jondurrant/IoTFanControlerW5000/schematic/IoTFanControl/IoTFanControl.kicad_sch

## KiCad design schematic/IoTFanControl/IoTFanControl.kicad_sch (2022-04-07, an earlier design)

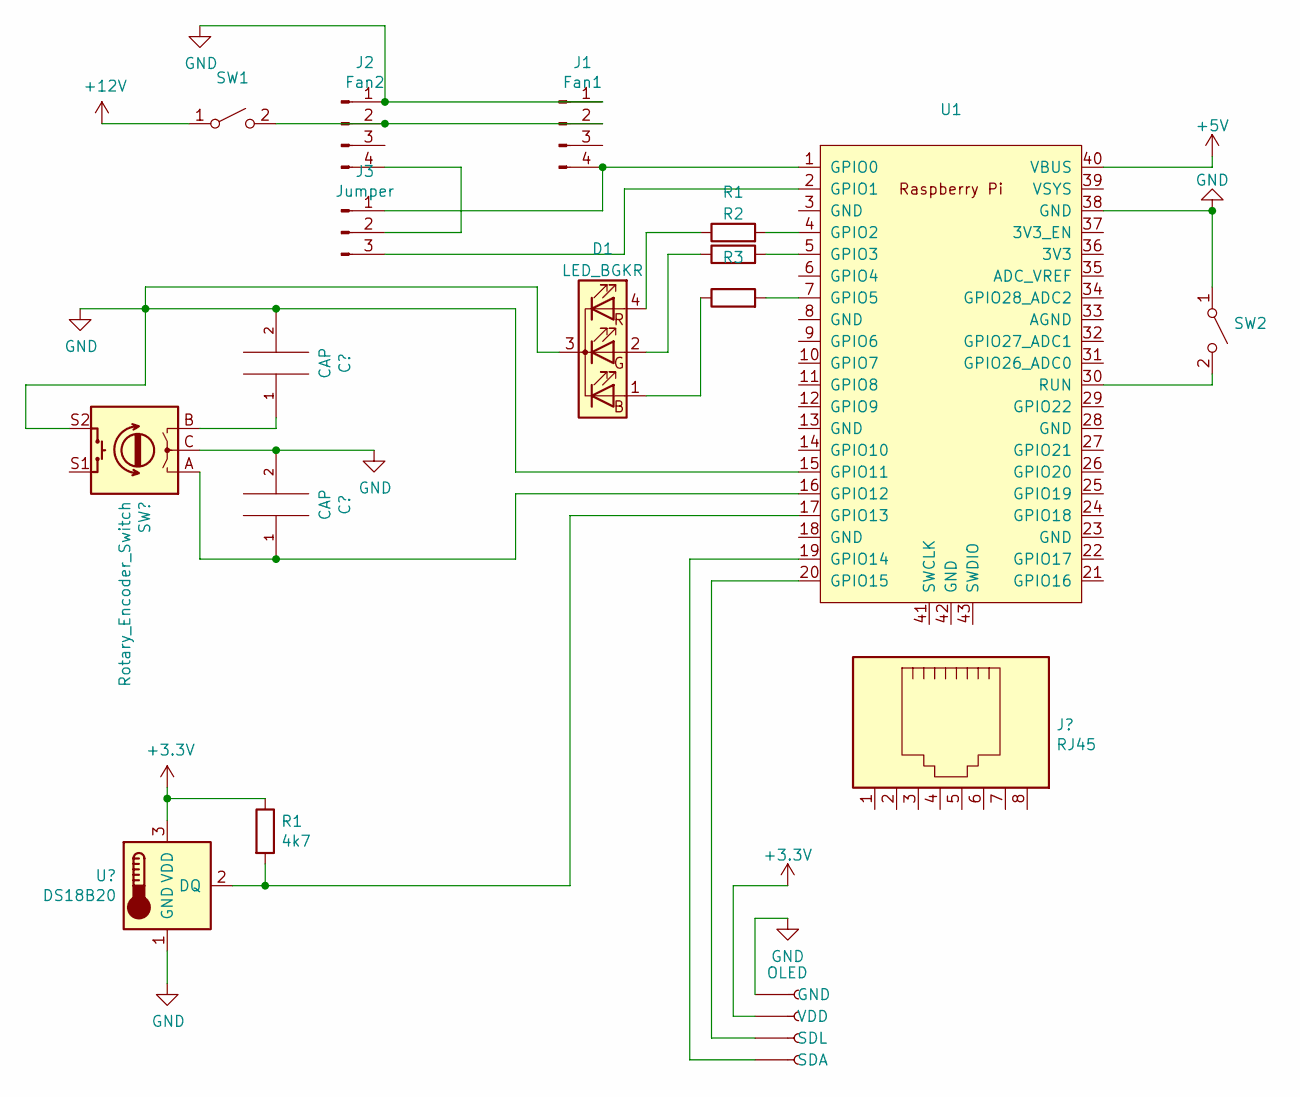
[picture p9: schematic IoTFanControl.kicad_sch]

Parts:
D1: LED_BGKR
J1: Fan1
J2: Fan2
J3: Jumper
OLED: Conn_01x04_Female
R1: 4k7
R2, R3: (no value)
SW1, SW2: (no value)
U1: (no value)

Connections:
unnamed: D1.1 (BA), R3.1
unnamed: D1.2 (GA), R2.1
unnamed: D1.3 (K), U1.15 (GPIO11)
unnamed: D1.4 (RA), R1.1
unnamed: J1.1, J2.1
unnamed: J1.2, J2.2, SW1.2 (B)
unnamed: J1.4, J3.1, U1.1 (GPIO0)
unnamed: J2.4, J3.2
unnamed: J3.3, U1.2 (GPIO1)
unnamed: OLED.3 (SDL), U1.20 (GPIO15)
unnamed: OLED.4 (SDA), U1.19 (GPIO14)
unnamed: R1.2, U1.4 (GPIO2), U1.17 (GPIO13)
unnamed: R2.2, U1.5 (GPIO3)
unnamed: R3.2, U1.7 (GPIO5)
unnamed: SW2.1 (A), U1.38 (GND)
unnamed: SW2.2 (B), U1.30 (RUN)
