jondurrant/IoTFanControlerW5000/src/FanLogging.h

/***
 * MQTTConfig.h
 * Configuration for IOT Fan
 * Jon Durrant
 * 21-Nov-2021
 */

#ifndef FAN_LOGGING_H__
#define FAN_LOGGING_H__

#define LIBRARY_LOG_NAME "IOT FAN"
#define LIBRARY_LOG_LEVEL LOG_INFO
#include <logging_stack.h>



#endif //FAN_LOGGING_H__
